frolbel/transistortester/Doku/trunk/pdftex/german/ttester.tex

\documentclass[pdftex,12pt,a4paper,oneside,english]{report}
\special{papersize=210mm,297mm}
\usepackage{lmodern}
\usepackage[T1]{fontenc}		%umlaute!
\usepackage[utf8x]{inputenc}
\usepackage[cm]{fullpage}
\usepackage[ngerman]{babel}
\usepackage[pdftex]{graphicx}
\usepackage[labelsep=period]{caption}
\usepackage{subcaption}
\usepackage{color}
\usepackage{fixltx2e}
\usepackage{epstopdf}
\usepackage{hyperref}
\usepackage{float}
\usepackage{circuitikz}
%\usepackage{subfig}
\graphicspath{{./FIG}}

\begin{document}
\ctikzset{bipoles/length=.6cm}
\ctikzset{bipoles/thickness=4}
\newcommand\electricC {
\hspace{-14 pt}
\begin{circuitikz}
\draw (0,0) to[capacitor] (0:1);
\end{circuitikz}
\hspace{-6 pt}
}
\newcommand\electricR {
\hspace{-14 pt}
\begin{circuitikz}
\draw (0,0) to[european resistor] (0:1);
\end{circuitikz}
\hspace{-6 pt}
}
\newcommand\electricL {
\hspace{-14 pt}
\begin{circuitikz}
\draw (0,0) 
 to[american inductor] (-1,0) 
;\end{circuitikz}
\hspace{-6 pt}
}
\newcommand\electricDAK {
\begin{circuitikz}
\draw (0,0) to[full diode] (0:1);
\end{circuitikz}
}
\newcommand\electricDKA {
\begin{circuitikz}
\draw (0,0) to[full diode] (180:1);
\end{circuitikz}
}
\title{TransistorTester mit AVR-Mikrocontroller \\
und ein wenig mehr\\
Version 1.13k \\
}
\author{Karl-Heinz Kübbeler\\
\texttt{kh\_kuebbeler@web.de}}
\date{\today}
\maketitle
\tableofcontents

\include{00-preface}

\include{10-features}

\include{20-hardware}

\include{30-manual}

\include{40-configuring}

\include{50-measurement}

 \include{51-semicon}
 \include{52-resistors}
 \include{53-capacitors}
 \include{54-inductors}
 \include{55-selftest}
 \include{56-frequency}

\include{60-generators}
\include{70-errors}
\include{80-special}
\include{90-todo}

\begin{thebibliography}{99}

\bibitem{Frejek}
Markus Frejek
\emph{AVR-Transistortester,}.
Embedded Projects Journal,
11. Ausgabe,
2011

\bibitem{ATmega8}
Atmel Corporation
\emph{8-bit AVR with 8KBytes In-System Programmable Flash - ATmega8(L),}.
Manual,
2486Z-AVR-02/11,
2011

\bibitem{ATmega168}
Atmel Corporation
\emph{8-bit AVR with 4/8/16/32KBytes In-System Programmable Flash - ATmega48 - ATmega328,}.
Manual,
8271D-AVR-05/11,
2011

\bibitem{AVR126}
Atmel Corporation
\emph{Atmel AVR126: ADC of megaAVR in Single Ended Mode,}.
Application Note,
8444A-AVR-10/11,
2011

\bibitem{AVR121}
Atmel Corporation
\emph{Atmel AVR121: Enhancing ADC resolution by oversampling,}.
Application Note,
8003A-AVR-09/05,
2005

\bibitem{LaTeX}
\url{http://en.wikibooks.org/wiki/LaTeX}
\emph{LaTeX documentation,}.
Guide to the LaTeX markup language,
2012

\bibitem{Gnuplot}
\url{http://en.wikibooks.org/wiki/Gnuplot}
\emph{Gnuplot documentation,}.
Documentation for the plotting tool gnuplot,
2012

\bibitem{ESR}
Wikipedia
\url{http://de.wikipedia.org/wiki/Equivalent_Series_Resistance}
\emph{Erläuterung zum ESR}.
Normung und Ersatzschaltbild eines Kondensators,
2012

\bibitem{Xfig}
\url{http://www.xfig.org/userman}
\emph{Xfig documentation,}.
Documentation of the interactive drawing tool xfig,
2009

\bibitem{gimp}
\url{http://docs.gimp.org/2.6/de}
\emph{gimp documentation}.
Documentation of the GNU Image Manipolation Program,
2010

\bibitem{markus1}
\url{http://www.mikrocontroller.net/articles/AVR-Transistortester}
\emph{Online Dokumentation des Transistortester,}
Online Article,
2009-2011

\bibitem{avrdude}
\url{http://www.mikrocontroller.net/articles/AVRDUDE}
\emph{Online Dokumentation des avrdude programmer interface,}
Online Article,
2004-2011

\bibitem{markus2}
\url{http://www.mikrocontroller.net/topic/131804}
\emph{Thread von Markus F.,}
Forum thread, 
2009

\bibitem{karlheinz1}
\url{http://www.mikrocontroller.net/articles/AVR\_Transistortester}
\emph{Kurze Eigenschaftenbeschreibung des TransistorTester von Karl-Heinz K.,}
Online Article,
2012

\bibitem{karlheinz2}
\url{http://www.mikrocontroller.net/topic/248078}
\emph{Thread von Karl-Heinz K.,}
Thread und Software Versionen,
2012

\bibitem{winavr1}
\url{http://www.mikrocontroller.net/articles/WinAVR}
\emph{Artikel über WinAVR,}
Online Artikel,
2012

\bibitem{winavr2}
\url{http://sourceforge.net/projects/winavr/files}
\emph{Quelle für WinAVR,}
Download Quelle,
2012

\bibitem{winavr3}
\url{http://www.mikrocontroller.net/topic/248078?page=5#2922341}
\emph{Patch für WinAVR, Setzen der Fuses mit avrdude,}
Download Quelle,
2012

\bibitem{st7565}
\url{http://www.orientdisplay.com/pdf/ST7565.pdf}
\emph{Datenblatt des grafischen Controllers ST7565,}
Download Quelle,
2014

\end{thebibliography}
\end{document}
