frolbel/transistortester/Doku/trunk/pdftex/russian/ttester.tex

\documentclass[12pt,a4paper,oneside,english]{report}
\special{papersize=210mm,297mm}
%\usepackage[T1]{fontenc}
%\usepackage[latin1]{inputenc}
\usepackage[cm]{fullpage}
\usepackage{cmap}
\usepackage[cp1251]{inputenc}
\usepackage[english,russian]{babel}
\usepackage[pdftex]{graphicx}
\usepackage{caption}
\usepackage{subcaption}
\usepackage{color}
\usepackage{fixltx2e}
\usepackage{epstopdf}
\usepackage{hyperref}
\usepackage{float}
\RequirePackage[labelsep=period]{caption}
\usepackage{circuitikz}
%\RequirePackage{caption}
%\usepackage{subfig}
\graphicspath{{./FIG}}

\begin{document}
\ctikzset{bipoles/length=.6cm}
\ctikzset{bipoles/thickness=4}
\newcommand\electricC {
\hspace{-14 pt}
\begin{circuitikz}
\draw (0,0) to[capacitor] (0:1);
\end{circuitikz}
\hspace{-6 pt}
}
\newcommand\electricR {
\hspace{-14 pt}
\begin{circuitikz}
\draw (0,0) to[european resistor] (0:1);
\end{circuitikz}
\hspace{-6 pt}
}
\newcommand\electricL {
\hspace{-14 pt}
\begin{circuitikz}
\draw (0,0) 
 to[american inductor] (-1,0) 
;\end{circuitikz}
\hspace{-6 pt}
}
\newcommand\electricDAK {
\begin{circuitikz}
\draw (0,0) to[full diode] (0:1);
\end{circuitikz}
}
\newcommand\electricDKA {
\begin{circuitikz}
\draw (0,0) to[full diode] (180:1);
\end{circuitikz}
}
\title{Тестер ЭРЭ с AVR микроконтроллером\\
и минимумом дополнительных элементов\\
Версия 1.13k \\
}
\author{Karl-Heinz K\"ubbeler\\
\texttt{kh\_kuebbeler@web.de}\\
\textbf{{\scriptsize русский перевод Сергей Базыкин}}}
\vspace{1cm}
\date{\today}
\maketitle
\tableofcontents

\include{00-preface}

\include{10-features}

\include{20-hardware}

\include{30-manual}

\include{40-configuring}

\include{50-measurement}

 \include{51-semicon}
 \include{52-resistors}
 \include{53-capacitors}
 \include{54-inductors}
 \include{55-selftest}
 \include{56-frequency}

\include{60-generators}
\include{70-errors}
\include{80-special}
\include{90-todo}

\begin{thebibliography}{99}

\bibitem{Frejek}
Markus Frejek
\emph{AVR-Transistortester,}.
Embedded Projects Journal,
11. Ausgabe,
2011

\bibitem{ATmega8}
Atmel Corporation
\emph{8-bit AVR with 8KBytes In-System Programmable Flash - ATmega8(L),}.
Руководство,
2486Z-AVR-02/11,
2011

\bibitem{ATmega168}
Atmel Corporation
\emph{8-bit AVR with 4/8/16/32KBytes In-System Programmable Flash - ATmega48 - ATmega328,}.
Руководство,
8271D-AVR-05/11,
2011

\bibitem{AVR126}
Atmel Corporation
\emph{Atmel AVR126: ADC of megaAVR in Single Ended Mode,}.
Замечания по применению,
8444A-AVR-10/11,
2011

\bibitem{AVR121}
Atmel Corporation
\emph{Atmel AVR121: Enhancing ADC resolution by oversampling,}.
Замечания по применению,
8003A-AVR-09/05,
2005

\bibitem{LaTeX}
\url{http://en.wikibooks.org/wiki/LaTeX}
\emph{Документация по LaTeX,}.
Руководство по языку разметки LaTeX,
2012

\bibitem{Gnuplot}
\url{http://en.wikibooks.org/wiki/Gnuplot}
\emph{Документация по Gnuplot,}.
Документация по инструменту построения Gnuplot,
2012

\bibitem{ESR}
Wikipedia
\url{http://de.wikipedia.org/wiki/Equivalent_Series_Resistance}
\emph{Что такое ESR на немецком языке}.
Стандартизация и эквивалентная схема конденсатора,
2012

\bibitem{Xfig}
\url{http://www.xfig.org/userman}
\emph{Документация по Xfig,}.
Документация инструмента интерактивного рисования Xfig,
2009

\bibitem{gimp}
\url{http://docs.gimp.org/2.6/de}
\emph{Документация по gimp}.
Документация программы Image Manipolation Program,
2010

\bibitem{markus1}
\url{http://www.mikrocontroller.net/articles/AVR-Transistortester}
\emph{Онлайн документация по Транзистор Тестеру,}
Интернет статья,
2009-2011

\bibitem{avrdude}
\url{http://www.mikrocontroller.net/articles/AVRDUDE}
\emph{Онлайн документация к интерфейсу avrdude программатора,}
Интернет статья,
2004-2011

\bibitem{markus2}
\url{http://www.mikrocontroller.net/topic/131804}
\emph{Тема Markus,}
Тема на форуме, 
2009

\bibitem{karlheinz1}
\url{http://www.mikrocontroller.net/articles/AVR\_Transistortester}
\emph{Краткое описание новых особенностей Транзистор Тестера Karl-Heinz K.,}
Интернет статья,
2012

\bibitem{karlheinz2}
\url{http://www.mikrocontroller.net/topic/248078}
\emph{Тема Karl-Heinz,}
Тема и новые версии микропрограммного обеспечения,
2012

\bibitem{winavr1}
\url{http://www.mikrocontroller.net/articles/WinAVR}
\emph{Информация о WinAVR на немецком языке,}
Интернет статья,
2012

\bibitem{winavr2}
\url{http://sourceforge.net/projects/winavr/files}
\emph{Исходники WinAVR пакетов,}
Ресурс для загрузки,
2012

\bibitem{winavr3}
\url{http://www.mikrocontroller.net/topic/248078?page=5#2922341}
\emph{Патч для WinAVR, установка фюзов в avrdude,}
Ресурс для загрузки,
2012

\bibitem{st7565}
\url{http://www.orientdisplay.com/pdf/ST7565.pdf}
\emph{Документация к графическому контроллеру ST7565,}
Ресурс для загрузки,
2014

\end{thebibliography}
\end{document}
