frolbel/transistortester/Doku/tags/ttester_eng107k.pdf

# TransistorTester with AVR microcontroller and a little more Version 1.07k

### Karl-Heinz K¨ubbeler

kh kuebbeler@web.de

### April 19, 2013

# Contents

1 Features | 4
2 Hardware | 7
3 Instructions for use | 14
4 Configuring the TransistorTester | 18
5 Description of the measurement procedures | 23

6 Known errors and unsolved problems | 70
7 Special Software Parts | 71
8 To Do List and new ideas | 72

## Preface

### Basically Motive

Every hobbyist knows the following problem: You disassemle a Transistor out of a printed board or you get one out of a collection box. If you find out the identification number and you already have a data sheet or you can get the documents about this part, everything is well. But if you don’t find any documents, you have no idea, what kind of part this can be. With conventional approach of measurement it is difficult and time-consuming to find out the type of the part and parameters. It could be a NPN, PNP, N- or P-Channel-Mosfet etc. It was the idea of Markus F. to hand over the work to a AVR microcontroller.
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
