frolbel/transistortester/Doku/tags/ttester_ger107k.pdf

# TransistorTester mit AVR-Mikrocontroller und ein wenig mehr Version 1.07k

### Karl-Heinz Kübbeler

kh_kuebbeler@web.de

### 19. April 2013

# Inhaltsverzeichnis

1 Eigenschaften | 5
2 Hardware | 8
3 Bedienungshinweise | 16
4 Konfigurieren des TransistorTesters | 20
5 Beschreibung des Messverfahrens | 25

6 Bekannte Fehler und ungelöste Probleme | 72
7 Spezielle Softwareteile | 73
8 Arbeitsliste und neue Ideen | 74

## Vorwort
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
