frolbel/transistortester/Doku/trunk/pdftex/PNG/charge_229uFalt.png

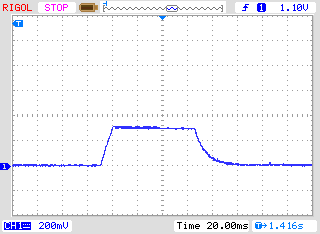
Doku/trunk/pdftex/PNG/charge_229uFalt.png
