frolbel/transistortester/Doku/tags/german/ttinfo_ger110k.pdf

# Kurzbeschreibung der Messungen mit dem Transistortester Version 1.10k

### Karl-Heinz Kübbeler

kh_kuebbeler@web.de

### 21. Januar 2014

# Inhaltsverzeichnis

1 Beschreibung der BJT-Messungen | 2
2 Beschreibung der MOSFET-Messungen | 6

# Kapitel 1

# Beschreibung der BJT-Messungen

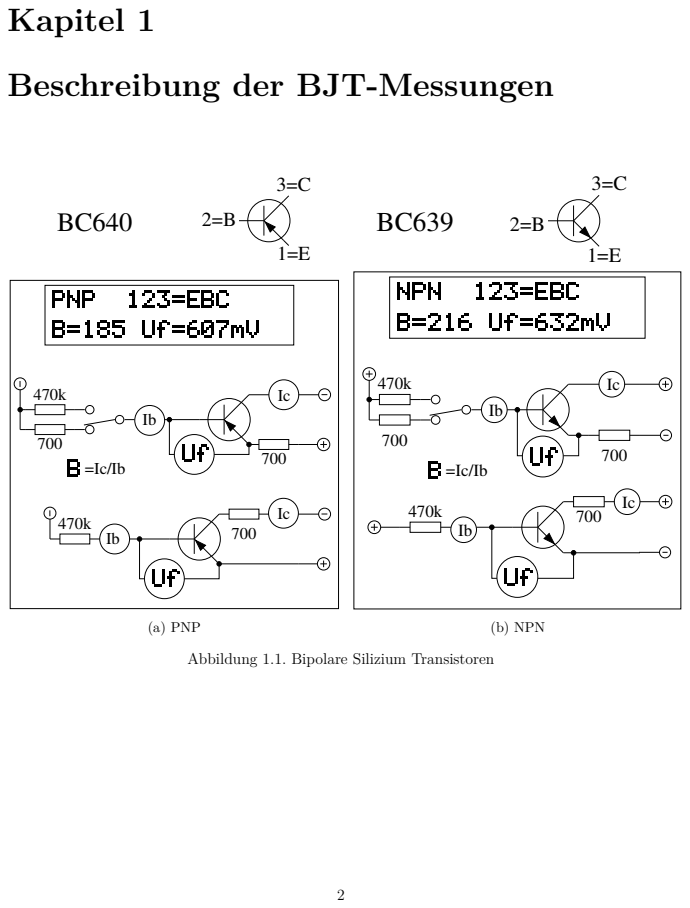
[picture p148: page 3]
(a) PNP; (b) NPN

Abbildung 1.1. Bipolare Silizium Transistoren

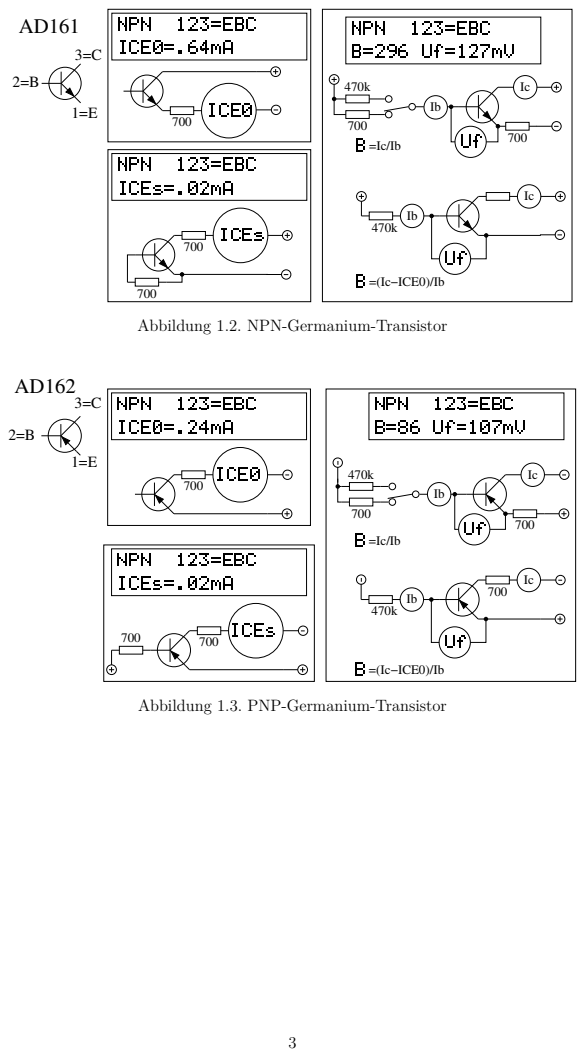
[picture p149: page 4]
=(Ic−ICE0)/Ib

Abbildung 1.2. NPN-Germanium-Transistor

Abbildung 1.3. PNP-Germanium-Transistor

BC516
BC517

(a) PNP; (b) NPN

Abbildung 1.4. Silizium Darlington-Transistoren

Abbildung 1.5. NPN-Transistor mit Diode und Widerstand

## BDV64C

## BDV65C

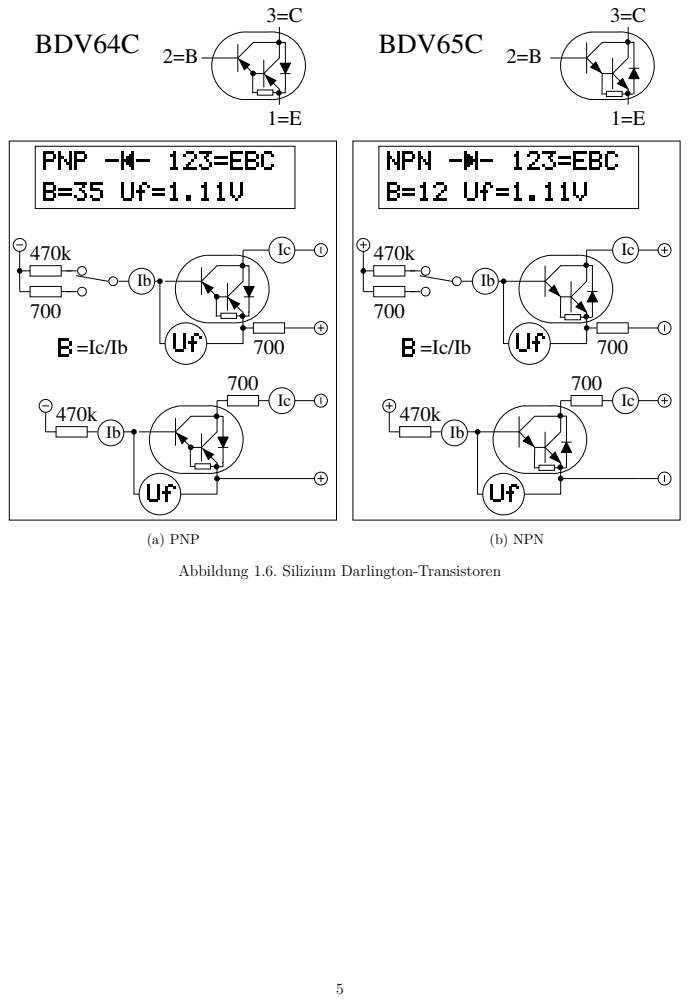
[picture p150: page 6]
(a) PNP; (b) NPN

Abbildung 1.6. Silizium Darlington-Transistoren

# Kapitel 2

# Beschreibung der MOSFET-Messungen

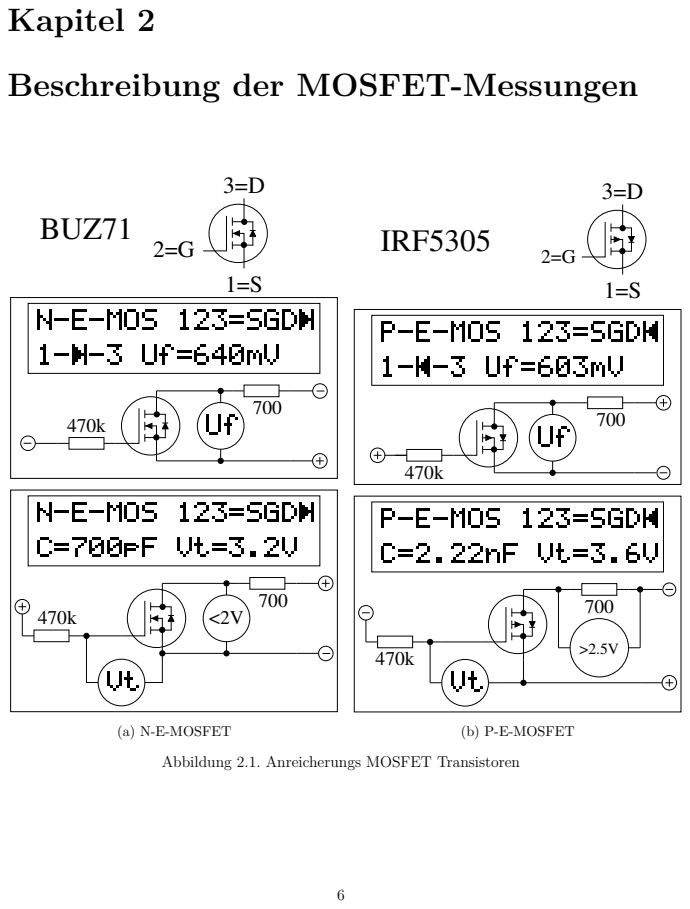
[picture p151: page 7]
BUZ71; (a) N-E-MOSFET; 2=G IRF5305; (b) P-E-MOSFET

Abbildung 2.1. Anreicherungs MOSFET Transistoren

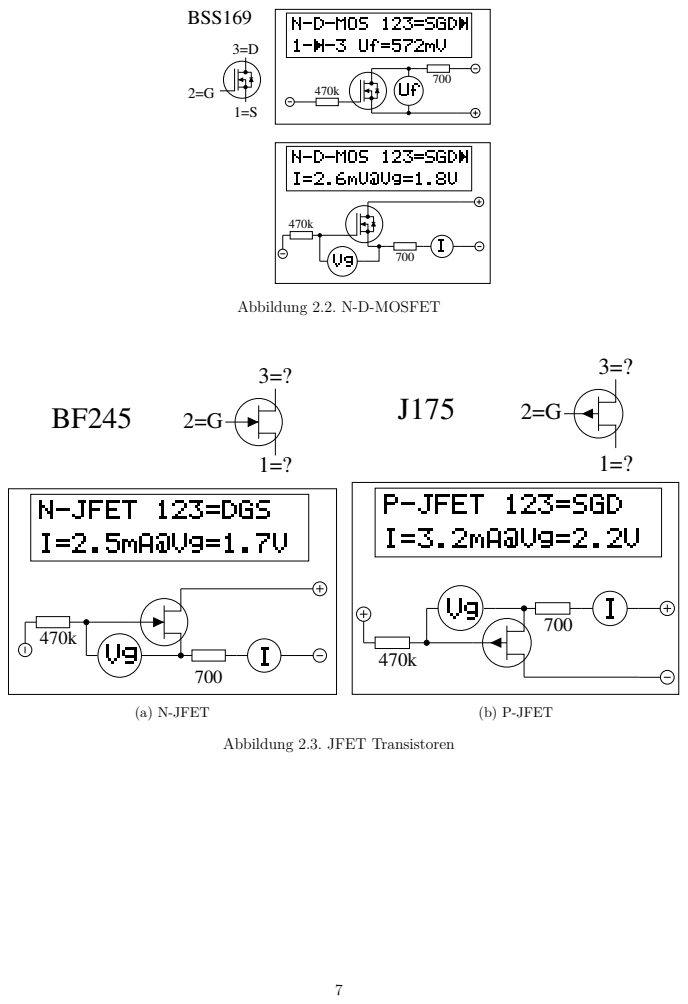
[picture p152: page 8]
BSS169; Abbildung 2.2. N-D-MOSFET; (a) N-JFET; (b) P-JFET

Abbildung 2.3. JFET Transistoren

# Literaturverzeichnis

[1] Markus Frejek AVR-Transistortester,. Embedded Projects Journal, 11. Ausgabe, 2011
[2] Atmel Corporation 8-bit AVR with 8KBytes In-System Programmable Flash - ATmega8(L),. Manual, 2486Z-AVR-02/11, 2011
[3] Atmel Corporation 8-bit AVR with 4/8/16/32KBytes In-System Programmable Flash - ATmega48 - ATmega328,. Manual, 8271D-AVR-05/11, 2011
[4] http://en.wikibooks.org/wiki/LaTeX LaTeX documentation,. Guide to the LaTeX markup language, 2012
[5] Wikipedia http://de.wikipedia.org/wiki/Equivalent_Series_Resistance Erläuterung zum ESR. Normung und Ersatzschaltbild eines Kondensators, 2012
[6] http://www.xfig.org/userman Xfig documentation,. Documentation of the interactive drawing tool xfig, 2009
[7] http://docs.gimp.org/2.6/de gimp documentation. Documentation of the GNU Image Manipolation Program, 2010
[8] http://www.mikrocontroller.net/articles/AVR-Transistortester Online Dokumentation des Transistortester, Online Article, 2009-2011
[9] http://www.mikrocontroller.net/articles/AVRDUDE Online Dokumentation des avrdude programmer interface, Online Article, 2004-2011
[10] http://www.mikrocontroller.net/topic/131804 Thread von Markus F., Forum thread, 2009
[11] http://www.mikrocontroller.net/articles/AVR_Transistortester Kurze Eigenschaftenbeschreibung des TransistorTester von Karl-Heinz K., Online Article, 2012
[12] http://www.mikrocontroller.net/topic/248078 Thread von Karl-Heinz K., Thread und Software Versionen, 2012
